gurues/PowerMeterDIY/Ayuda_Montaje/01_Placa Power Meter DIY 4 Canales.jpg

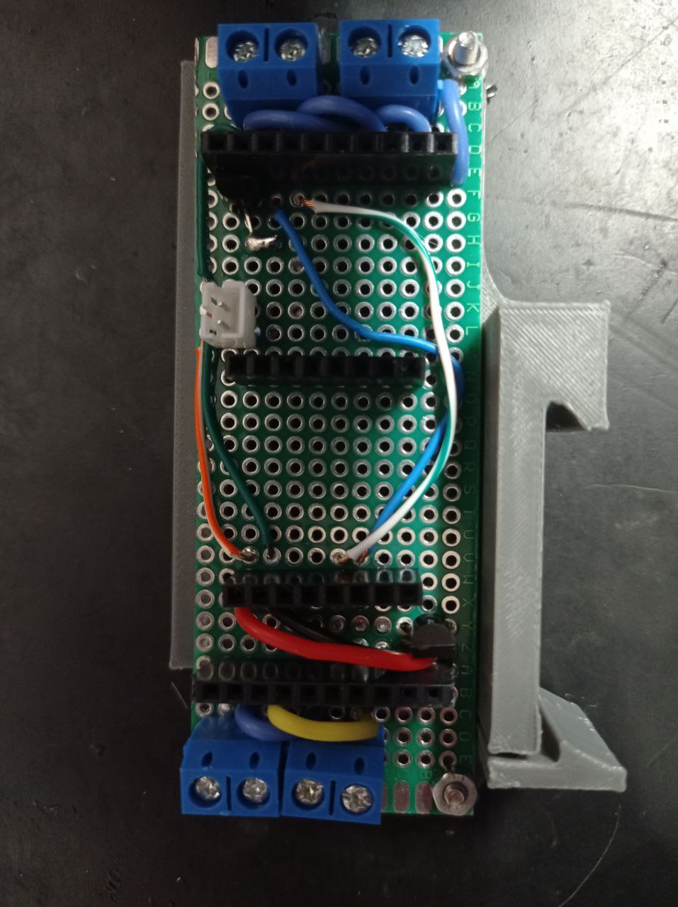
Ayuda_Montaje/01_Placa Power Meter DIY 4 Canales.jpg
