gurues/PowerMeterDIY/Ayuda_Montaje/Esquema_Montaje.jpg

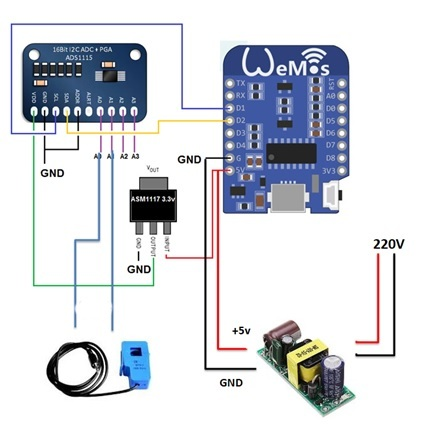
Ayuda_Montaje/Esquema_Montaje.jpg
